ensar-hodzic/US2024-KATANE/predati/slave_pico/potenciometar.py

from machine import Pin, ADC, Timer

# IZBACENO IZ POSLJEDNJE PREDAJE :(

class Potenciometar:
    potencimetar_values = [ 10, 30, 50, 20, 40, 60, 70, 0]
    T = 100
    eps = 5 # tolerancija 
    # pins - broj pina za potenciometar
    def __init__(self, state, pins):
        self.solved = False
        self.potenciometar = ADC(pins[0])
        self.sifra = self.potencimetar_values[state]
        self.timerPot = Timer(mode=Timer.PERIODIC, period=self.T, callback=self.PotenciometarGame)


    def PotenciometarGame(self, t):
        print(int(self.potenciometar.read_u16()/65535*100))
        if abs(int(self.potenciometar.read_u16()/65535*100) - self.sifra) < self.eps:
            print("BRAVO NO BOMBA KAPUT ON POTENCIOMETAR GAME")
            self.timerPot.deinit()
            self.solved = True

    def solved(self):
        return self.solved

    def get_sifra(self):
        return self.sifra
            
