ensar-hodzic/US2024-KATANE/connect.py

# Raspberry master

# spoji se na internet
import network
import time
from machine import Pin
from umqtt.robust import MQTTClient
import ujson


network_name = 'Wifi'
network_password = 'password'

nic = network.WLAN(network.STA_IF)
nic.activate(True)
nic.connect(network_name, network_password)

while not nic.isconnected():
    print('Cekam vezu')
    time.sleep(1)



# okini RGB randomiser

state = rgb_randomiser()



# daj konfiguraciju slaveu



# pokreni igru
